ak66666/ThumbsUpV10/Photos/IMG_20240502_160216887_HDR.jpg

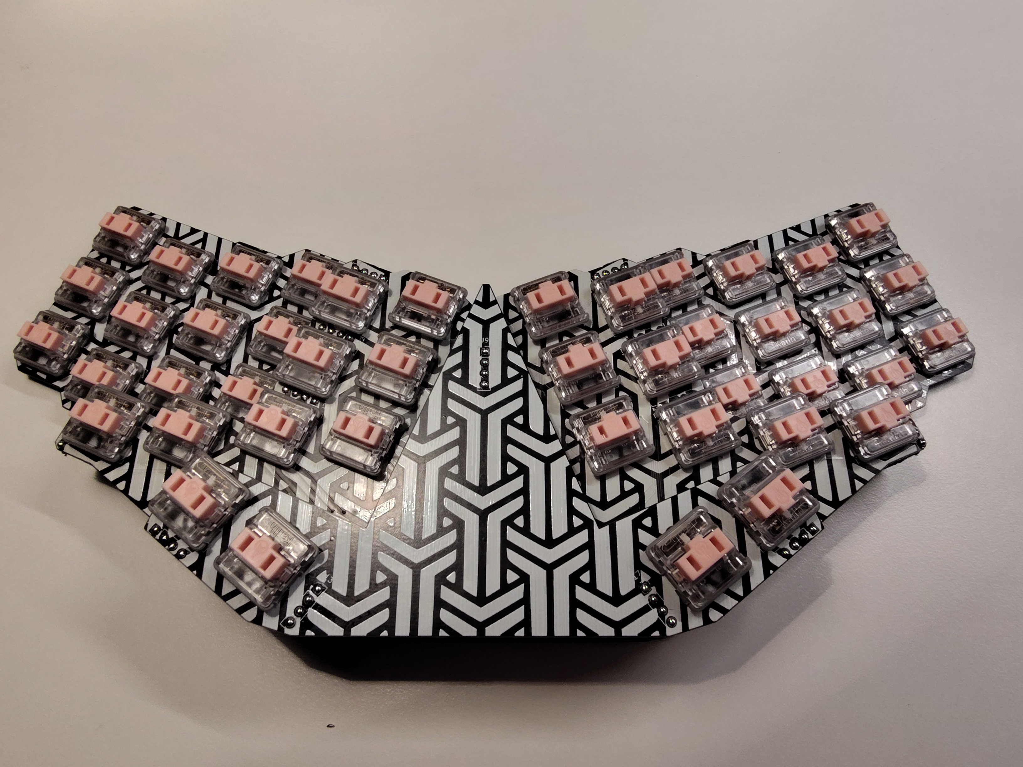
Photos/IMG_20240502_160216887_HDR.jpg
