ak66666/ThumbsUpV10/Photos/IMG_20240502_160226921.jpg

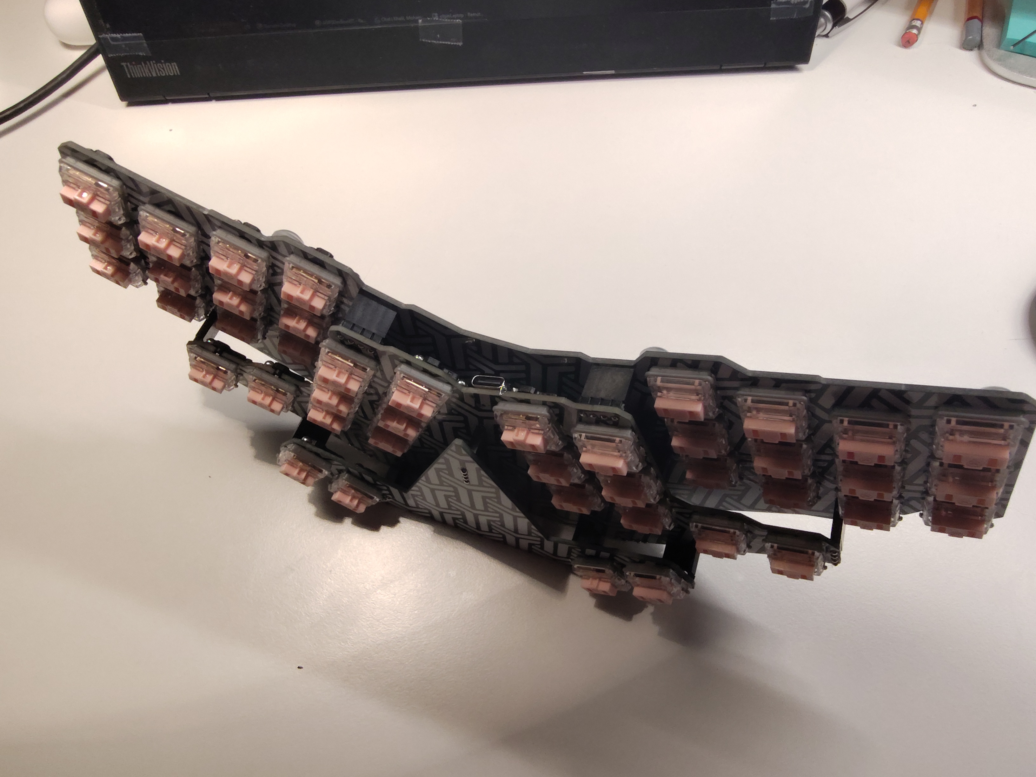
Photos/IMG_20240502_160226921.jpg
