ak66666/ThumbsUpV10/Photos/IMG_20240502_160238988.jpg

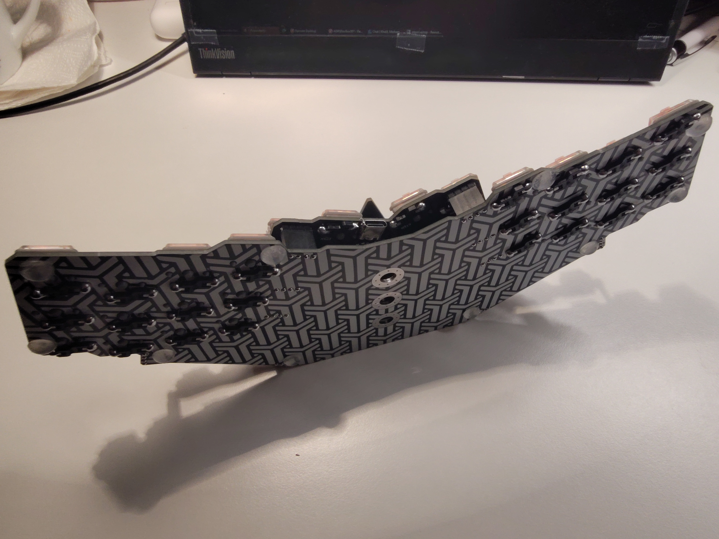
Photos/IMG_20240502_160238988.jpg
