ak66666/ThumbsUpV10/Photos/IMG_20240502_213121297_HDR.jpg

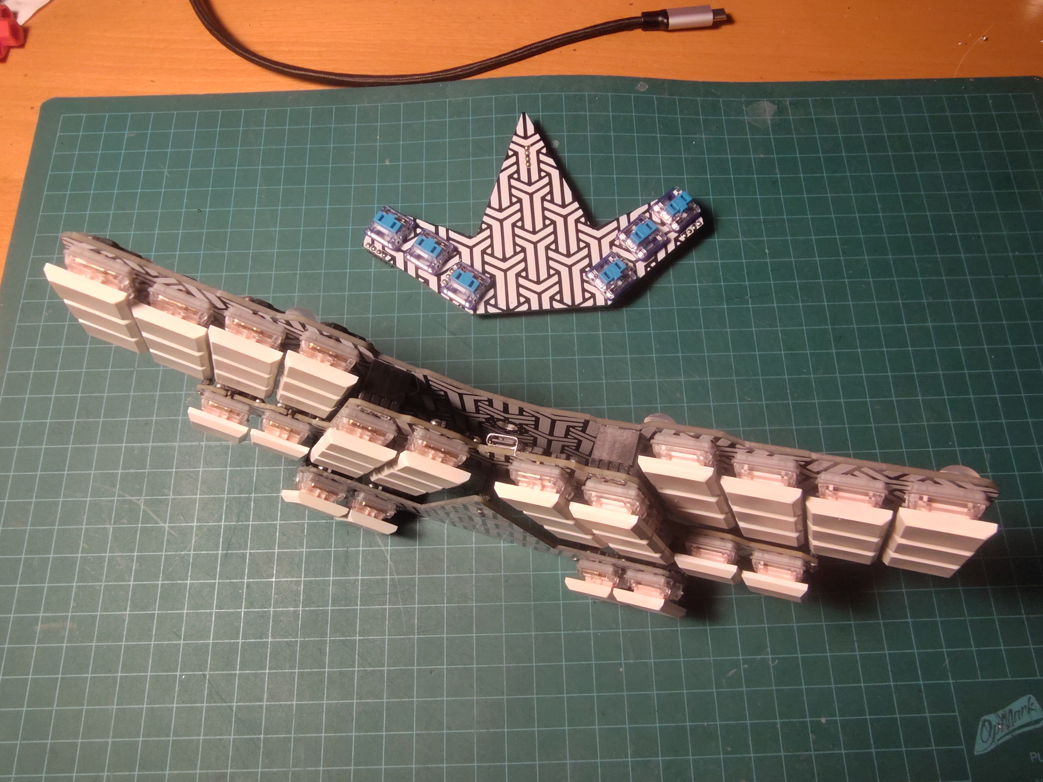
Photos/IMG_20240502_213121297_HDR.jpg
