ak66666/ThumbsUpV10/Photos/IMG_20240502_213134879_HDR.jpg

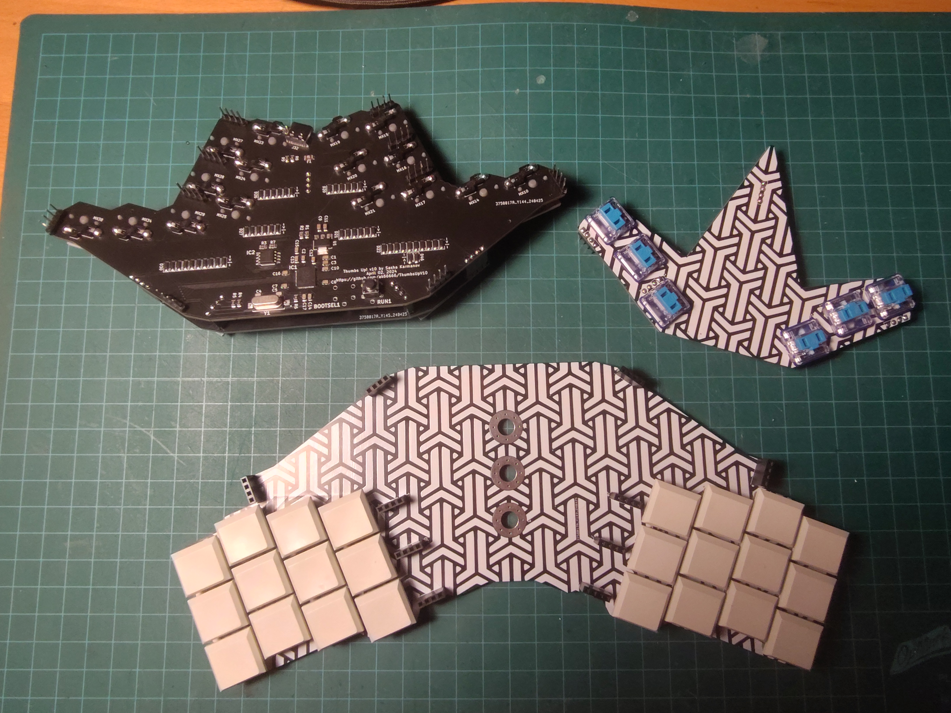
Photos/IMG_20240502_213134879_HDR.jpg
