ak66666/ThumbsUpV10/Photos/IMG_20240502_213235107_HDR.jpg

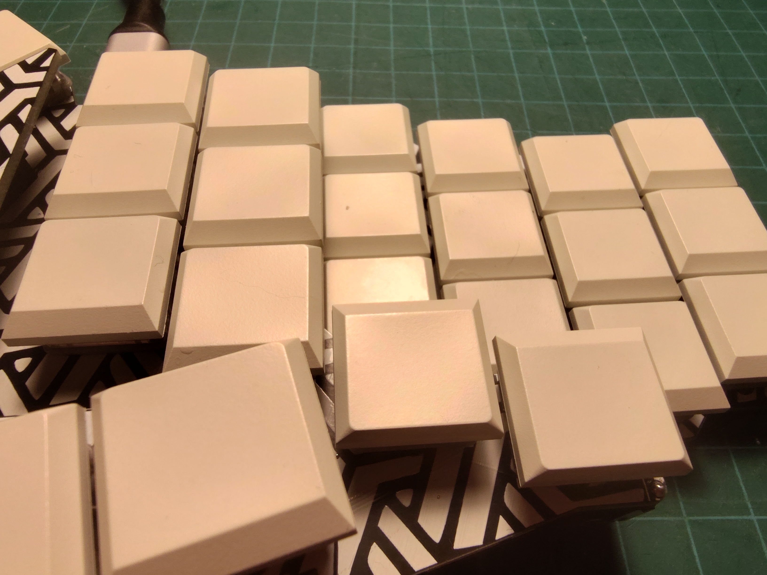
Photos/IMG_20240502_213235107_HDR.jpg
