ak66666/ThumbsUpV10/Silkscreens/44 Key Keyboard Layout 20 pct.png

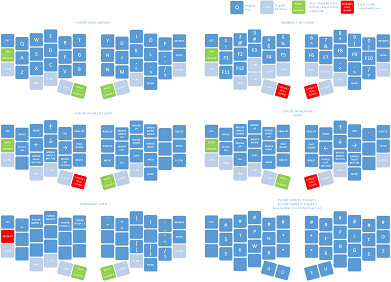
Silkscreens/44 Key Keyboard Layout 20 pct.png
