ak66666/ThumbsUpV10/Silkscreens/Pattern.png

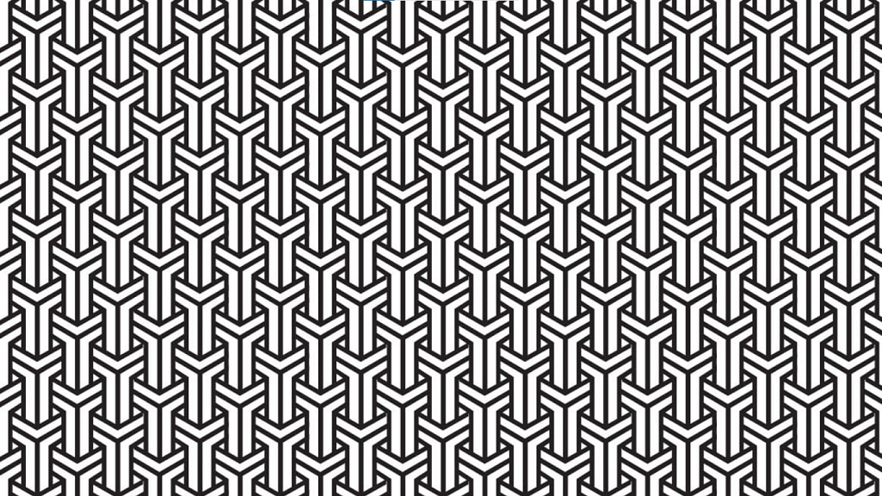
Silkscreens/Pattern.png
