ak66666/ThumbsUpV10/Silkscreens/QWERTY.png

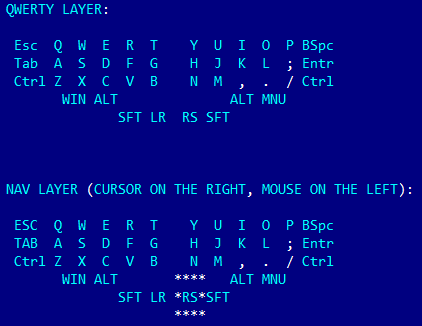
Silkscreens/QWERTY.png
